MohamedAlDeep/RGB-Mechanical-KEEB-/IMAGES/ALIEXRESS_CART.png

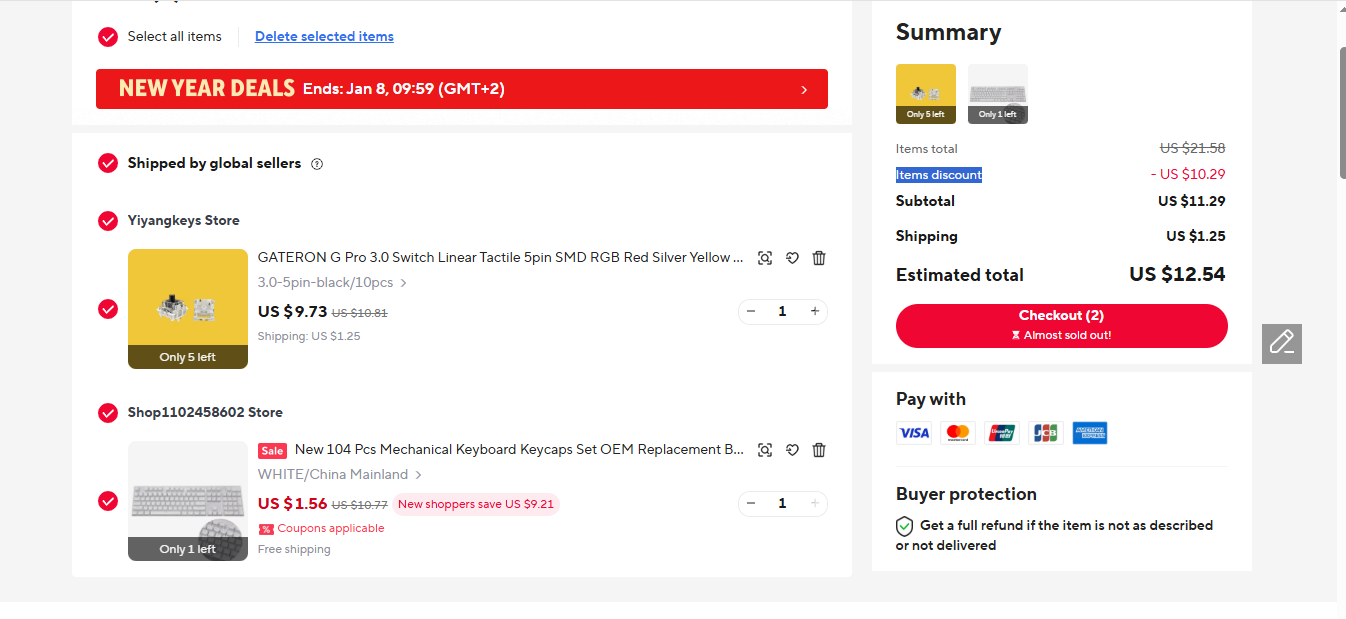
IMAGES/ALIEXRESS_CART.png
