MohamedAlDeep/RGB-Mechanical-KEEB-/IMAGES/PCB_CART.png

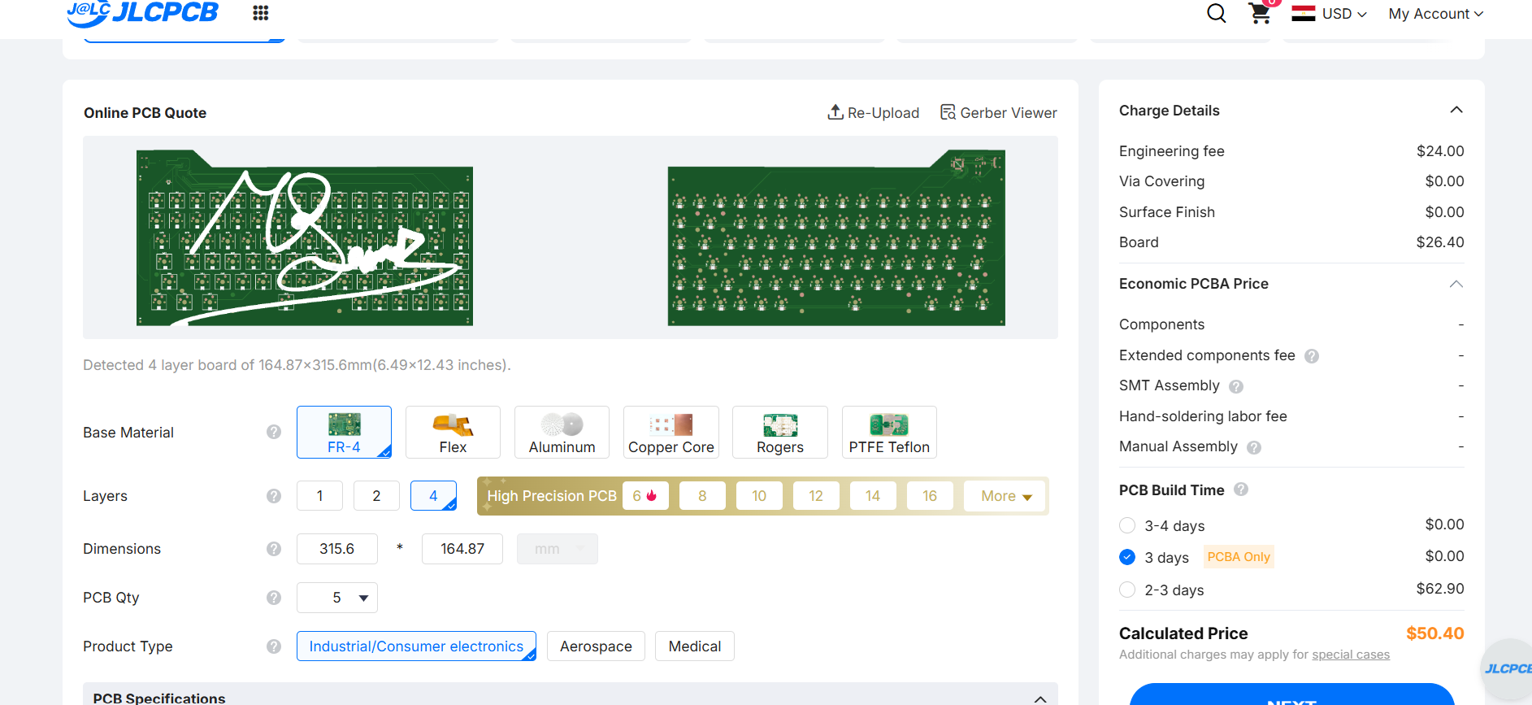
IMAGES/PCB_CART.png
